chl33/Room133/Ebox/gui.scad

// Copyright (c) 2026 Chris Lee and contributors.
// Licensed under the MIT license. See LICENSE file in the project root for details.

// :GUI:
leak_check = false;
// :GUI:
oled = true;
// :GUI:
mount_tab = true;
// :GUI:
motion_light = true;
// :GUI:
motion = false;
// :GUI:
radar = false;
// :GUI:
show_vitamins = true;
// :GUI:
show_box = true;
// :GUI:
top = true;
